axlzys/KH-Tester/Software/ServoTest.py

#!/usr/bin/python
from Adafruit_MotorHAT import Adafruit_MotorHAT, Adafruit_DCMotor

import time
import atexit

# create a default object, no changes to I2C address or frequency
mh = Adafruit_MotorHAT(addr=0x60,freq=50)

# recommended for auto-disabling motors on shutdown!
def turnOffMotors():
    mh.getMotor(1).run(Adafruit_MotorHAT.RELEASE)
    mh.getMotor(2).run(Adafruit_MotorHAT.RELEASE)
    mh.getMotor(3).run(Adafruit_MotorHAT.RELEASE)
    mh.getMotor(4).run(Adafruit_MotorHAT.RELEASE)

atexit.register(turnOffMotors)

################################# DC motor test!
myMotor = mh.getMotor(3)
s1 = mh.getServo(0)
print("**************\n")
while (True):
  # Change speed of continuous servo on channel O
  s1.write(20)
  time.sleep(1)
  s1.write(120)
  time.sleep(1)
  print("-----------\n")
